mcusim/Xling/hardware/output/xling_v4.1_board.png

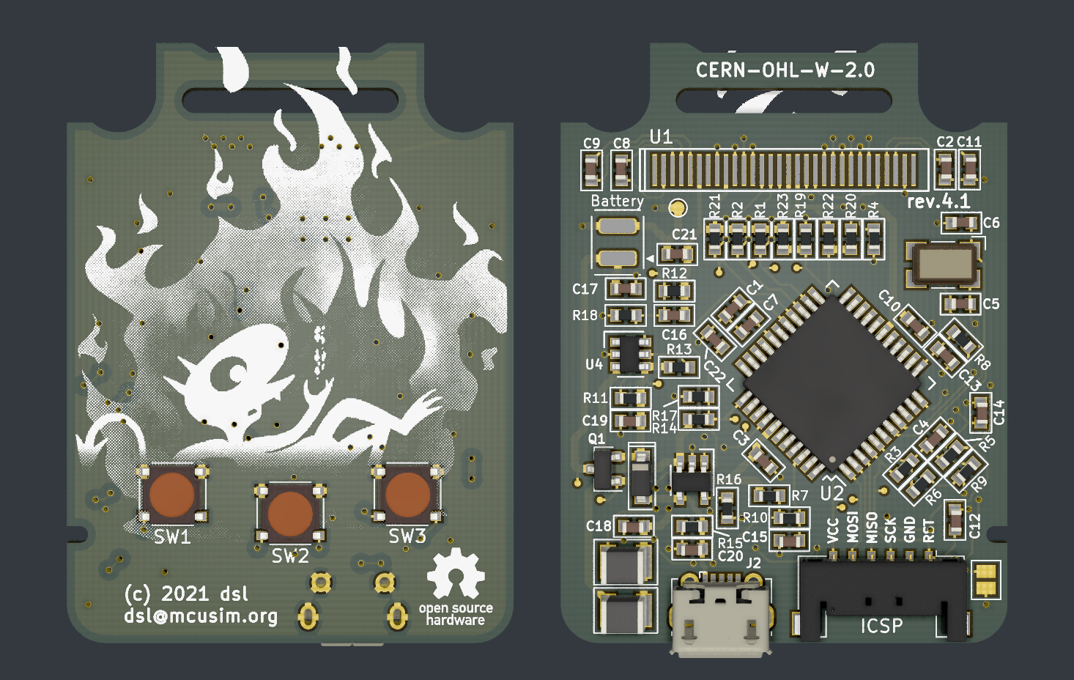
hardware/output/xling_v4.1_board.png
