mcusim/Xling/hardware/3d_models/packages/AP3401.stp

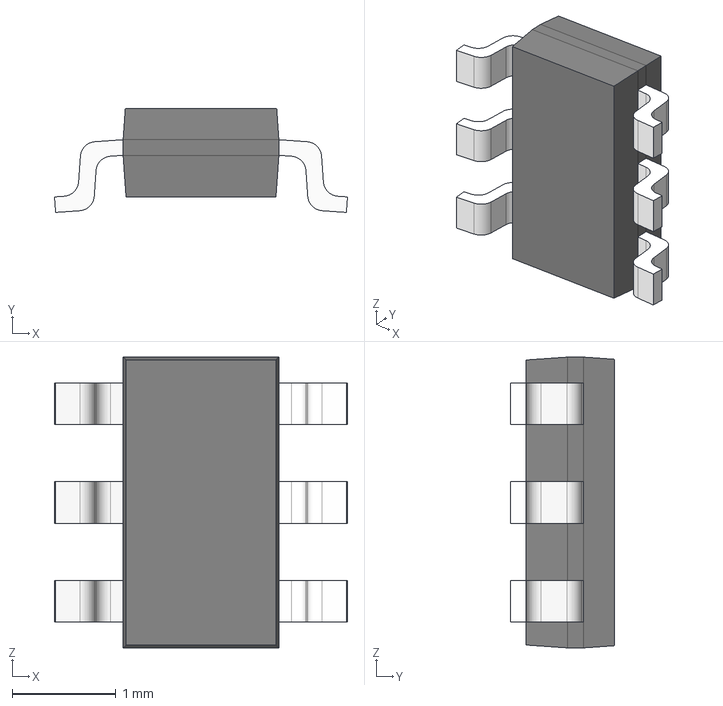
[picture p16: CAD file, 2019-11-17]
hardware/3d_models/packages/AP3401.stp
2.82 x 1.00 x 2.80 mm
