mcusim/Xling/software/src/xling/display_task.c

/*-
 * SPDX-License-Identifier: GPL-3.0-or-later
 *
 * This file is part of a firmware for Xling, a tamagotchi-like toy.
 *
 * Copyright (c) 2019, 2020 Dmitry Salychev
 *
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
 * You should have received a copy of the GNU General Public License
 * along with this program.  If not, see <https://www.gnu.org/licenses/>.
 */
#include <stdint.h>
#include <stdio.h>
#include <stdlib.h>
#include <string.h>
#include <limits.h>
#include <time.h>
#include <avr/io.h>
#include <avr/interrupt.h>
#include <avr/pgmspace.h>
#include <util/delay.h>

/*
 * A display task.
 *
 * It is supposed to be the only task which updates the display.
 *
 * NOTE: An interrupt of the 16-bit Timer 3 and its compare-match channel A is
 * used to resume the display updating task.
 */

/* FreeRTOS headers. */
#include "FreeRTOS.h"
#include "task.h"
#include "queue.h"

/* SH1106 driver headers. */
#include "mcusim/drivers/avr-gcc/avr/display/sh1106/sh1106.h"

/* Xling headers. */
#include "xling/tasks.h"
#include "xling/graphics.h"
#include "xling/scenes/scenes.h"
#include "xling/font/Alagard_12pt.h"

/*
 * ----------------------------------------------------------------------------
 * Local types.
 * ----------------------------------------------------------------------------
 */

/*
 * This structure helps to process messages received from the task queue in a
 * separate function and keep their values.
 */
typedef struct msg_params_t {
	uint16_t	bat_lvl;
	uint16_t	bat_stat;
} msg_params_t;

/*
 * ----------------------------------------------------------------------------
 * Local macros.
 * ----------------------------------------------------------------------------
 */
#define SET_BIT(byte, bit)	((byte) |= (1U << (bit)))
#define CLEAR_BIT(byte, bit)	((byte) &= (uint8_t) ~(1U << (bit)))
#define TASK_NAME		"Display Task"
#define TASK_PERIOD		(42) /* in ms (~ 23.8 Hz) */
#define TASK_DELAY		(pdMS_TO_TICKS(TASK_PERIOD))
#define TEXT_BUFSZ		(128)

/*
 * Bigger stack size is necessary to draw text and images to the canvas which
 * will be moved to the display memory.
 */
#define STACK_SZ		(configMINIMAL_STACK_SIZE * 2)

/*
 * ----------------------------------------------------------------------------
 * Local variables.
 * ----------------------------------------------------------------------------
 */

/*
 * Configuration of the OLED display driver.
 */
static const MSIM_SH1106DrvConf_t _driver_conf = {
	.port_spi = &PORTB,		/* I/O port with SPI. */
	.ddr_spi = &DDRB,		/* DDR for the I/O port with SPI. */
	.mosi = PB5,			/* OLED SPI pin. */
	.miso = PB6,			/* OLED SPI pin. */
	.sck = PB7,			/* OLED SPI pin. */
};

/*
 * Configuration of the OLED display.
 */
static const MSIM_SH1106Conf_t _display_conf = {
	.rst_port = &PORTC,
	.rst_ddr = &DDRC,
	.cs_port = &PORTC,
	.cs_ddr = &DDRC,
	.dc_port = &PORTC,
	.dc_ddr = &DDRC,
	.rst = PC6,			/* OLED Reset pin. */
	.cs = PC7,			/* OLED Chip Select pin. */
	.dc = PC5,			/* OLED Data/Command pin. */
};

static volatile TaskHandle_t _task_handle;

/*
 * NOTE: 1024 bytes is enough to describe a monochrome image for OLED display
 *       which resolution is 128x64 px.
 */
static uint8_t _display_buffer[1024];

static XG_Canvas_t _canvas = {
	.data = &_display_buffer[0],
	.width = 128,
	.height = 64,
	.data_size = 8,
};

static char _text_buf[TEXT_BUFSZ];
static XG_Text_t _text = {
	.font = &XG_FONT_Alagard_12pt,
	.text = &_text_buf[0],
};

/*
 * ----------------------------------------------------------------------------
 * Local functions declarations.
 * ----------------------------------------------------------------------------
 */
static void	display_task(void *arg) __attribute__((noreturn));
static void	receive_msgs(const QueueHandle_t q,
                             MSIM_SH1106_t * const display,
                             msg_params_t *params);

int
XG_InitDisplayTask(XG_TaskArgs_t *arg, UBaseType_t priority,
                   TaskHandle_t *task_handle)
{
	BaseType_t stat;
	int rc = 0;

	/*
	 * Configure the display and its driver. We don't have to worry about
	 * interrupts and FreeRTOS scheduler - they shouldn't be active at the
	 * moment.
	 */
	{
		/* Keep CS high. Display isn't selected by default. */
		SET_BIT(PORTC, _display_conf.cs);

		/* Power On the display. */
		CLEAR_BIT(PORTC, _display_conf.rst);
		_delay_ms(1);
		SET_BIT(PORTC, _display_conf.rst);
		_delay_ms(10);

		/* Start the driver for SH1106-based displays. */
		MSIM_SH1106__drvStart(&_driver_conf);
	}

	/* Create the display task. */
	stat = xTaskCreate(display_task, TASK_NAME, STACK_SZ,
	                   arg, priority, task_handle);

	if (stat != pdPASS) {
		/* Sleep mode task couldn't be created. */
		rc = 1;
	} else {
		/* Task has been created successfully. */
		_task_handle = (*task_handle);
	}

	return rc;
}

static void
display_task(void *arg)
{
	const XG_TaskArgs_t * const args = (XG_TaskArgs_t *) arg;
	MSIM_SH1106_t * const display = MSIM_SH1106_Init(&_display_conf);
	TickType_t ticks;
	TickType_t delay = 0;
	TickType_t last_wake;
	msg_params_t params = {
		.bat_lvl = 100,
		.bat_stat = 0,
	};
	XG_Point_t pt = { 0, 0 };

	/* Use current time as a seed for random generator. */
	srand((unsigned int) time(NULL));

	/* Setup an OLED display. */
	MSIM_SH1106_DisplayOff(display);
	MSIM_SH1106_SetContrast(display, 0x75);
	MSIM_SH1106_DisplayNormal(display);
	MSIM_SH1106_SetScanDirection(display, 0);
	MSIM_SH1106_DisplayOn(display);
	MSIM_SH1106_bufSend(display);

	/* Remember the last wake time. */
	last_wake = xTaskGetTickCount();

	/* Task loop */
	while (1) {
		/* Wait for the next task tick. */
		vTaskDelayUntil(&last_wake, TASK_DELAY);

		/* Remember a moment in time. */
		ticks = xTaskGetTickCount();

		/*
		 * Receive and process all of the messages available in the
		 * display queue at the moment.
		 */
		receive_msgs(args->display_info.queue_handle, display, &params);

		/* Clear the canvas. */
		memset(_display_buffer, 0x00, 1024);

		/*
		 * Draw the frame time, battery level and battery status on
		 * the display.
		 */
		snprintf(_text_buf, TEXT_BUFSZ, "%lu ms", delay);
		pt.x = 85;
		pt.y = 20;
		XG_Print(&_canvas, &_text, pt);

		snprintf(_text_buf, TEXT_BUFSZ, "%u%%",
		         params.bat_lvl);
		pt.y = 31;
		XG_Print(&_canvas, &_text, pt);

		snprintf(_text_buf, TEXT_BUFSZ, (params.bat_stat == 1)
		         ? "yes" : "no");
		pt.y = 42;
		XG_Print(&_canvas, &_text, pt);

		pt.x = 0;
		pt.y = 0;
		//XG_Draw_PF(&_canvas, &XG_IMG_text_decoration, pt);
		XG_DrawScene(&_canvas, &XG_SCN_smoking_02);

		/* Transfer canvas buffer to the display. */
		XG_TransferCanvas(display, &_canvas);

		/*
		 * Calculate a delay to receive a message from the queue and
		 * draw an animation frame.
		 */
		delay = xTaskGetTickCount() - ticks;
	}

	/*
	 * The task must be deleted before reaching the end of its
	 * implementating function.
	 *
	 * NOTE: Shouldn't reach this point!
	 */
	vTaskDelete(NULL);
}

static void
receive_msgs(const QueueHandle_t q, MSIM_SH1106_t * const display,
             msg_params_t *params)
{
	static uint8_t bat_lvl_skip = 5;
	XG_Msg_t msg;
	BaseType_t status;

	/* Receive all of the messages from the queue. */
	while (1) {
		/* An attempt to receive the next message. */
		status = xQueueReceive(q, &msg, 0);

		/* Message has been received. */
		if (status == pdPASS) {
			switch (msg.type) {
			case XG_MSG_BATLVL:
				/* Skip several values initially. */
				if (bat_lvl_skip > 0) {
					bat_lvl_skip--;
				} else if (msg.value > 100) {
					params->bat_lvl = 100;
				} else {
					params->bat_lvl = msg.value;
				}

				break;
			case XG_MSG_BATSTATPIN:
				params->bat_stat = msg.value;
				break;
			case XG_MSG_TASKSUSP_REQ:
				/* Switch the display off. */
				MSIM_SH1106_bufClear(display);
				MSIM_SH1106_DisplayOff(display);
				MSIM_SH1106_bufSend(display);
				MSIM_SH1106_Wait(display);

				/*
				 * Block the task indefinitely to wait
				 * for a notification.
				 */
				xTaskNotifyWait(0, 0, NULL,
				                portMAX_DELAY);

				/* Switch the display back on. */
				MSIM_SH1106_bufClear(display);
				MSIM_SH1106_DisplayOn(display);
				MSIM_SH1106_bufSend(display);
				MSIM_SH1106_Wait(display);

				/*
				 * Skip the first battery level
				 * messages after awake.
				 */
				bat_lvl_skip = 5;

				break;
			default:
				/* Ignore other messages silently. */
				break;
			}
		} else {
			/*
			 * Queue is empty. There is no need to receive
			 * new messages anymore in this frame cycle.
			 */
			break;
		}
	}
}
