mcusim/Xling/software/include/rtos/portmacro.h

/*
 * FreeRTOS Kernel V10.2.1
 * Copyright (C) 2019 Amazon.com, Inc. or its affiliates.  All Rights Reserved.
 *
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
 * http://www.FreeRTOS.org
 * http://aws.amazon.com/freertos
 *
 * 1 tab == 4 spaces!
 */

/*
Changes from V1.2.3

	+ portCPU_CLOSK_HZ definition changed to 8MHz base 10, previously it
	  base 16.
*/

#ifndef PORTMACRO_H
#define PORTMACRO_H

#ifdef __cplusplus
extern "C" {
#endif

/*-----------------------------------------------------------
 * Port specific definitions.
 *
 * The settings in this file configure FreeRTOS correctly for the
 * given hardware and compiler.
 *
 * These settings should not be altered.
 *-----------------------------------------------------------
 */

/* Type definitions. */
#define portCHAR		char
#define portFLOAT		float
#define portDOUBLE		double
#define portLONG		long
#define portSHORT		int
#define portSTACK_TYPE	uint8_t
#define portBASE_TYPE	char

typedef portSTACK_TYPE StackType_t;
typedef signed char BaseType_t;
typedef unsigned char UBaseType_t;

#if( configUSE_16_BIT_TICKS == 1 )
	typedef uint16_t TickType_t;
	#define portMAX_DELAY ( TickType_t ) 0xffff
#else
	typedef uint32_t TickType_t;
	#define portMAX_DELAY ( TickType_t ) 0xffffffffUL
#endif
/*-----------------------------------------------------------*/

/* Critical section management. */
#define portENTER_CRITICAL()		asm volatile ( "in		__tmp_reg__, __SREG__" :: );	\
									asm volatile ( "cli" :: );								\
									asm volatile ( "push	__tmp_reg__" :: )

#define portEXIT_CRITICAL()			asm volatile ( "pop		__tmp_reg__" :: );				\
									asm volatile ( "out		__SREG__, __tmp_reg__" :: )

#define portDISABLE_INTERRUPTS()	asm volatile ( "cli" :: );
#define portENABLE_INTERRUPTS()		asm volatile ( "sei" :: );
/*-----------------------------------------------------------*/

/* Architecture specifics. */
#define portSTACK_GROWTH			( -1 )
#define portTICK_PERIOD_MS			( ( TickType_t ) 1000 / configTICK_RATE_HZ )
#define portBYTE_ALIGNMENT			1
#define portNOP()					asm volatile ( "nop" );
/*-----------------------------------------------------------*/

/* Kernel utilities. */
extern void vPortYield( void ) __attribute__ ( ( naked ) );
#define portYIELD()		vPortYield()
#define portYIELD_FROM_ISR()	vPortYield()
/*-----------------------------------------------------------*/

/* Task function macros as described on the FreeRTOS.org WEB site. */
#define portTASK_FUNCTION_PROTO( vFunction, pvParameters ) void vFunction( void *pvParameters )
#define portTASK_FUNCTION( vFunction, pvParameters ) void vFunction( void *pvParameters )

#ifdef __cplusplus
}
#endif

#endif /* PORTMACRO_H */
